etocancipa/Taller-Ingenieria-Electronica.-Grupo-Tumaquito-/PCB Tumaquito/Librerias/step/ky-037-microphone-module-1.snapshot.3/KY-037_.9.jpg

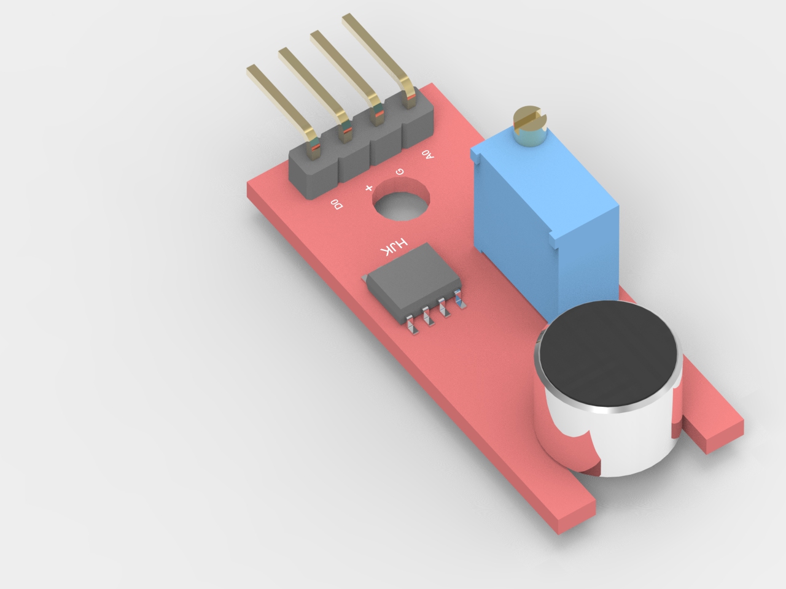
PCB Tumaquito/Librerias/step/ky-037-microphone-module-1.snapshot.3/KY-037_.9.jpg
