etocancipa/Taller-Ingenieria-Electronica.-Grupo-Tumaquito-/PCB Tumaquito/PDF Tumaquito/Proyecto 2-F_Cu.pdf

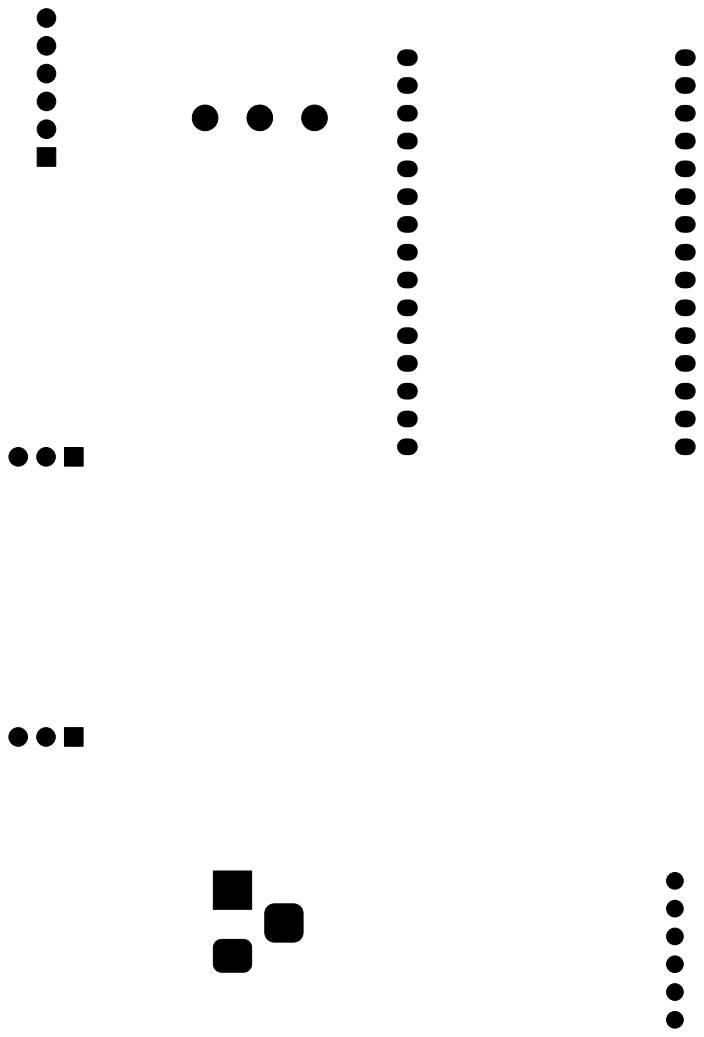
[picture p58: page 1]
