etocancipa/Taller-Ingenieria-Electronica.-Grupo-Tumaquito-/PCB Tumaquito/PDF Tumaquito/Proyecto 2-F_Mask.pdf

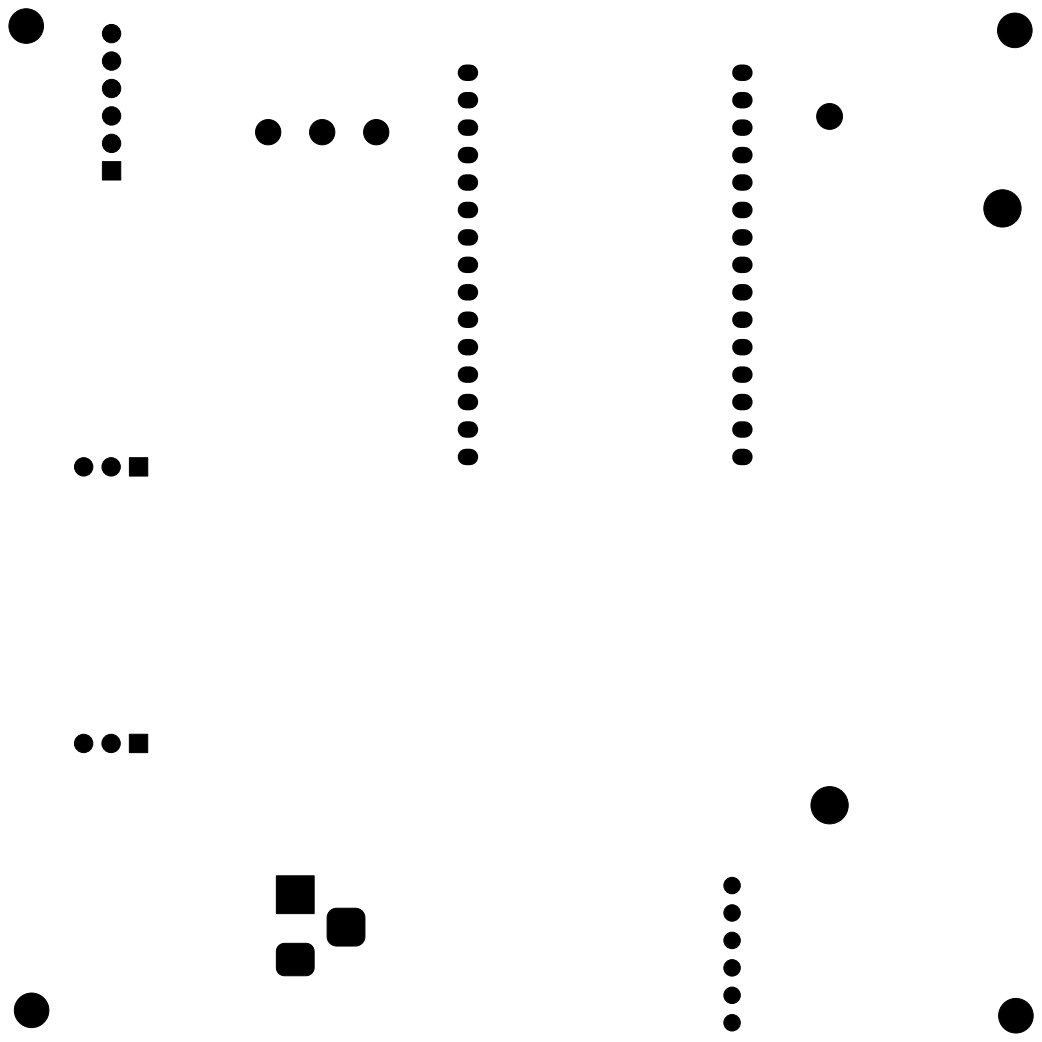
[picture p59: page 1]
