etocancipa/Taller-Ingenieria-Electronica.-Grupo-Tumaquito-/PCB Tumaquito/PDF Tumaquito/Proyecto 2-F_Silkscreen.pdf

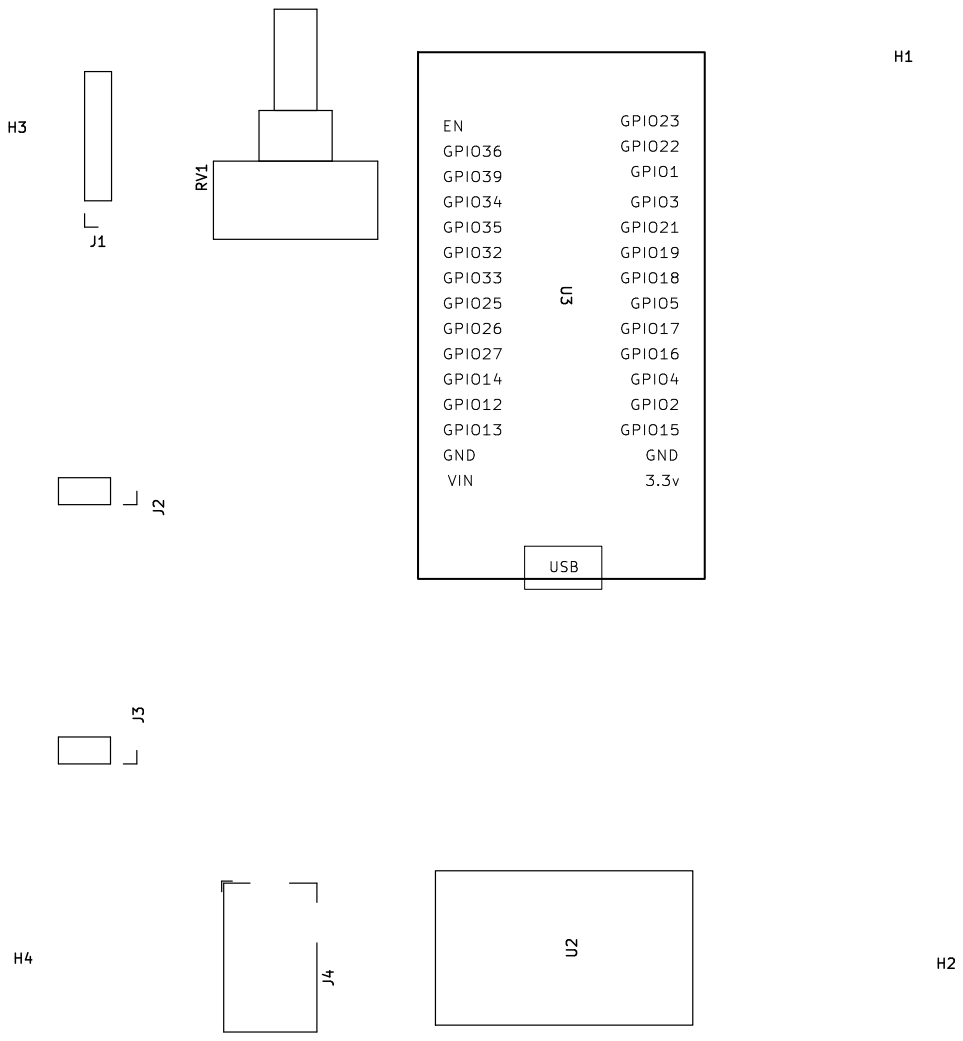
[picture p60: page 1]
